Settorezero/Supplino/media/supplino_off.jpg

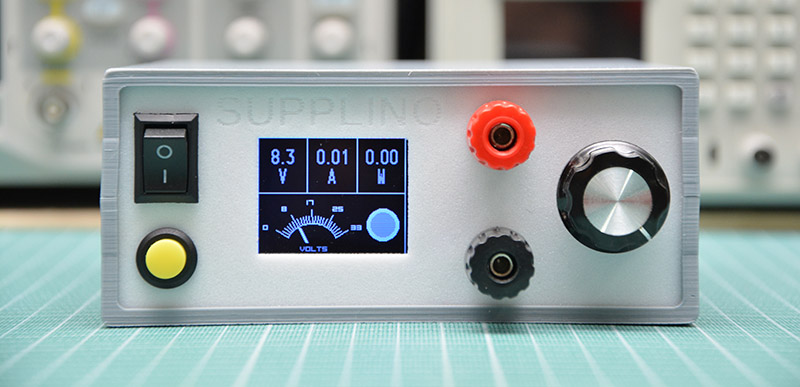
media/supplino_off.jpg
